landonr/homeThing/docs/groupTDisplay.gif

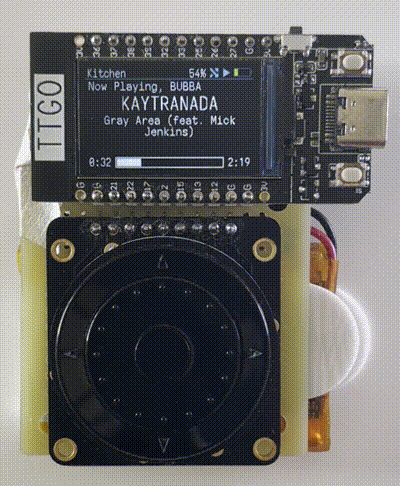
docs/groupTDisplay.gif
