landonr/homeThing/docs/m5stackFire.jpg

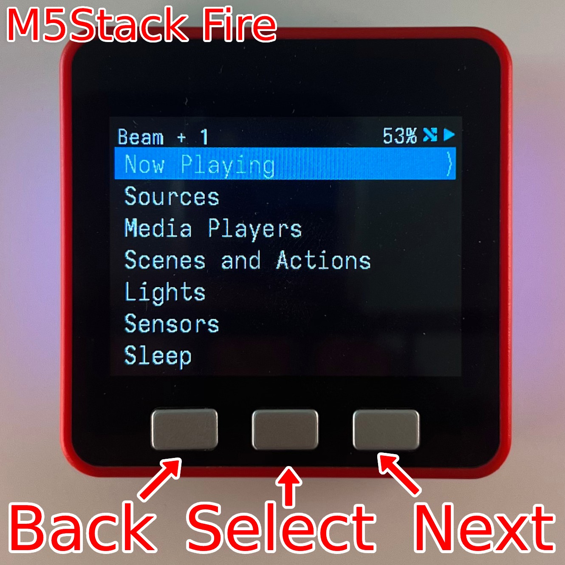
docs/m5stackFire.jpg
