landonr/homeThing/docs/m5StackFireBoot.gif

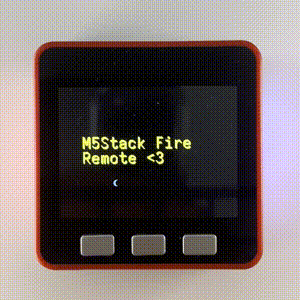
docs/m5StackFireBoot.gif
