landonr/homeThing/docs/nowPlayingOptions.jpg

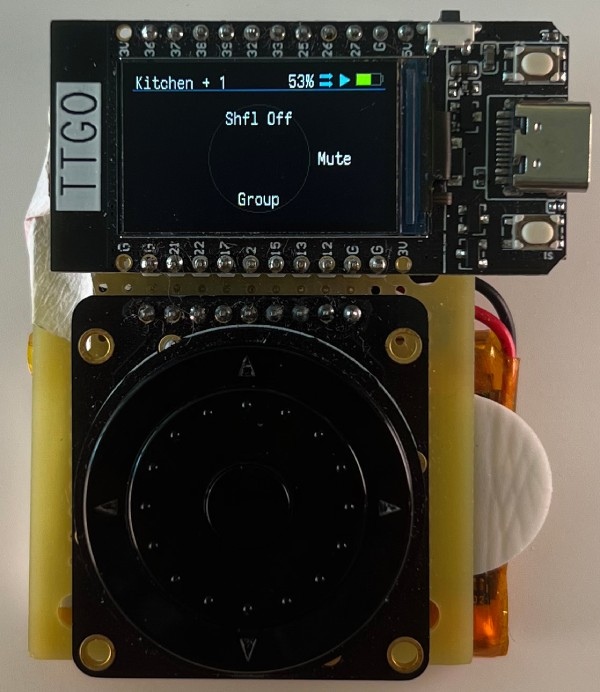
docs/nowPlayingOptions.jpg
