landonr/homeThing/docs/pausePlayFire.gif

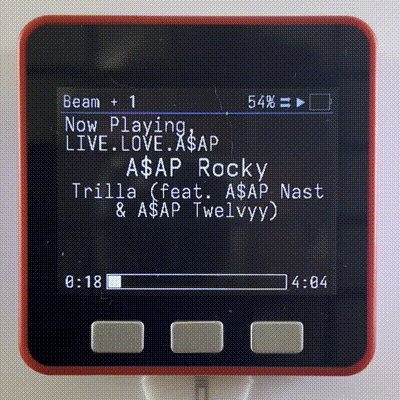
docs/pausePlayFire.gif
