landonr/homeThing/docs/scrollListSelectFire.gif

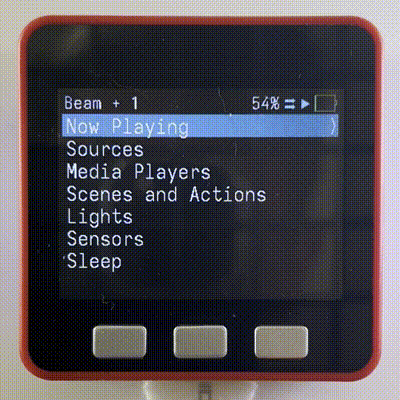
docs/scrollListSelectFire.gif
