landonr/homeThing/docs/sensors.jpg

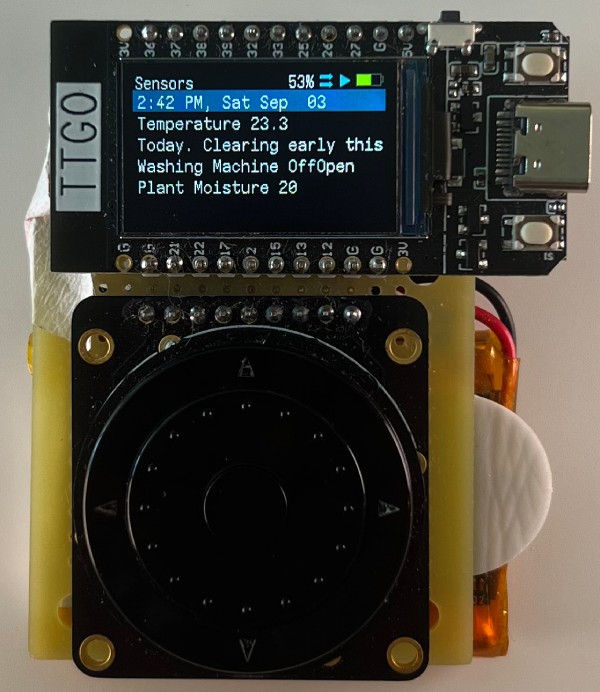
docs/sensors.jpg
