landonr/homeThing/docs/tdisplayOverlay.jpg

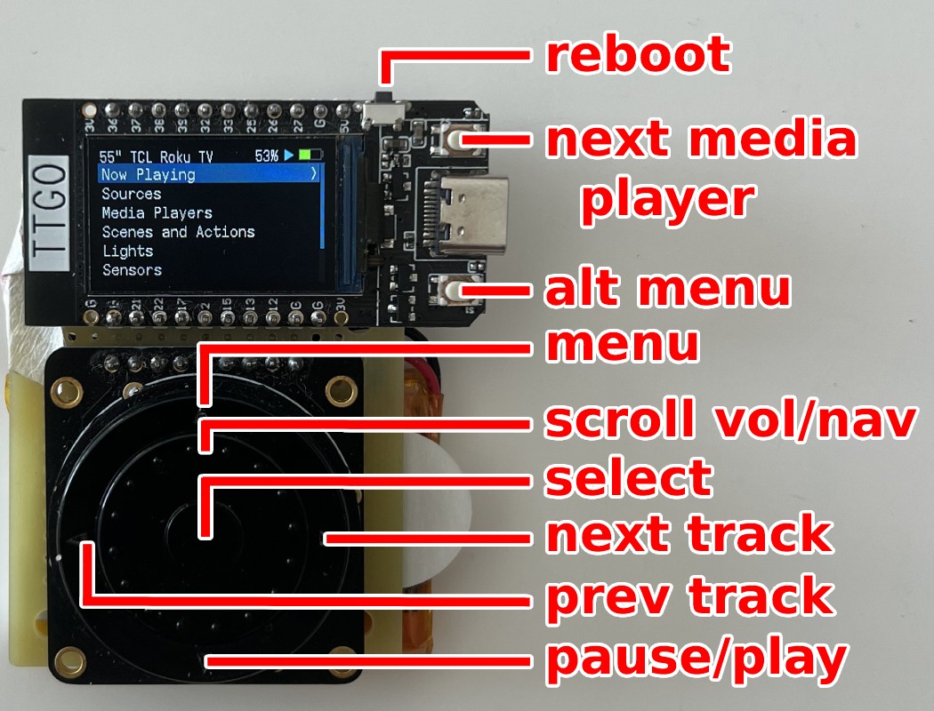
docs/tdisplayOverlay.jpg
