landonr/homeThing/Case Design/tdisplay/Case_v1.1B_--_Button_Set_--_FDM_--_mm.stl

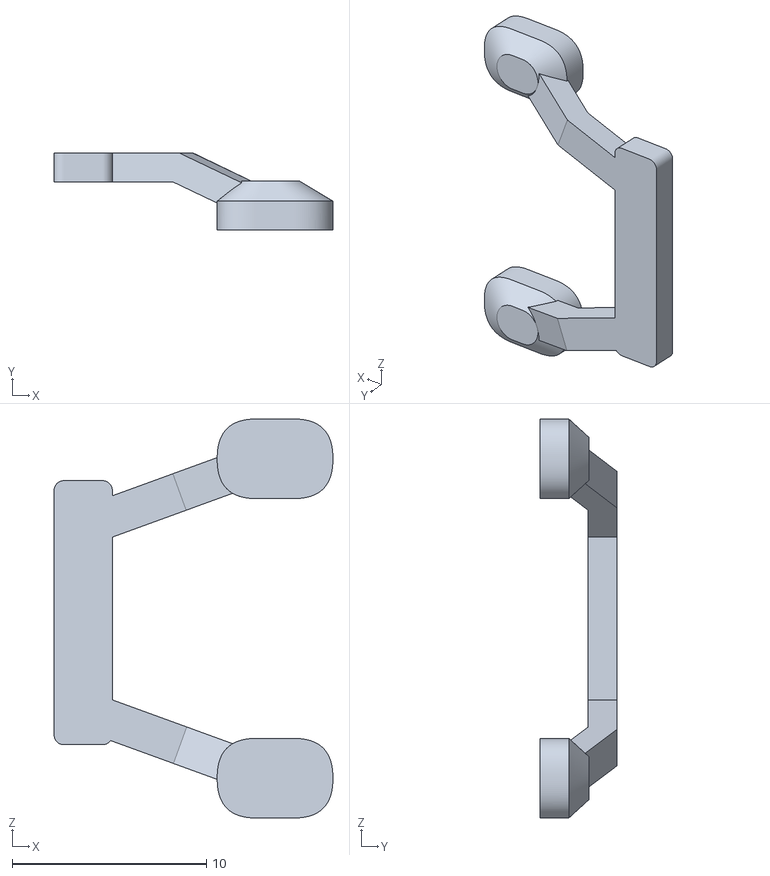
[picture p35: CAD file, 2023-03-23]
Case Design/tdisplay/Case_v1.1B_--_Button_Set_--_FDM_--_mm.stl
14.4 x 3.99 x 20.5
