landonr/homeThing/Case Design/tdisplay/Case_v1.1B_--_Front_Case_--_FDM_--_mm.stl

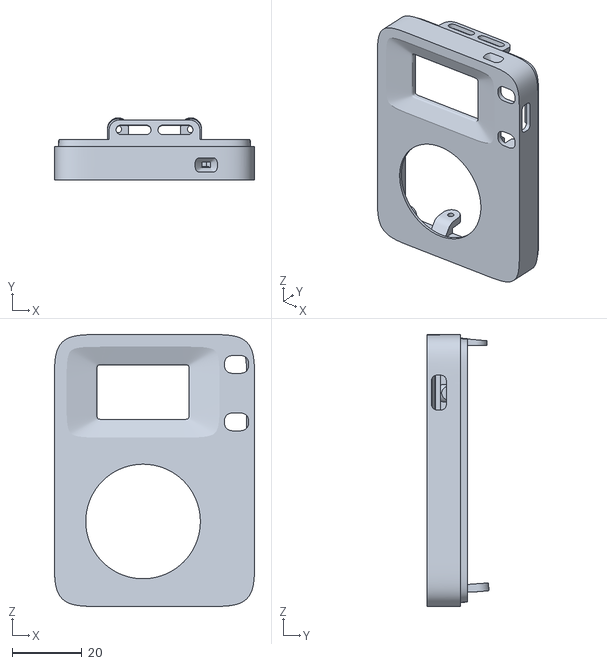
[picture p36: CAD file, 2023-03-23]
Case Design/tdisplay/Case_v1.1B_--_Front_Case_--_FDM_--_mm.stl
57.4 x 17.9 x 77.9
