landonr/homeThing/Case Design/tdisplay/Case_v1.1B_--_Back_Case_--_FDM_--_mm.stl

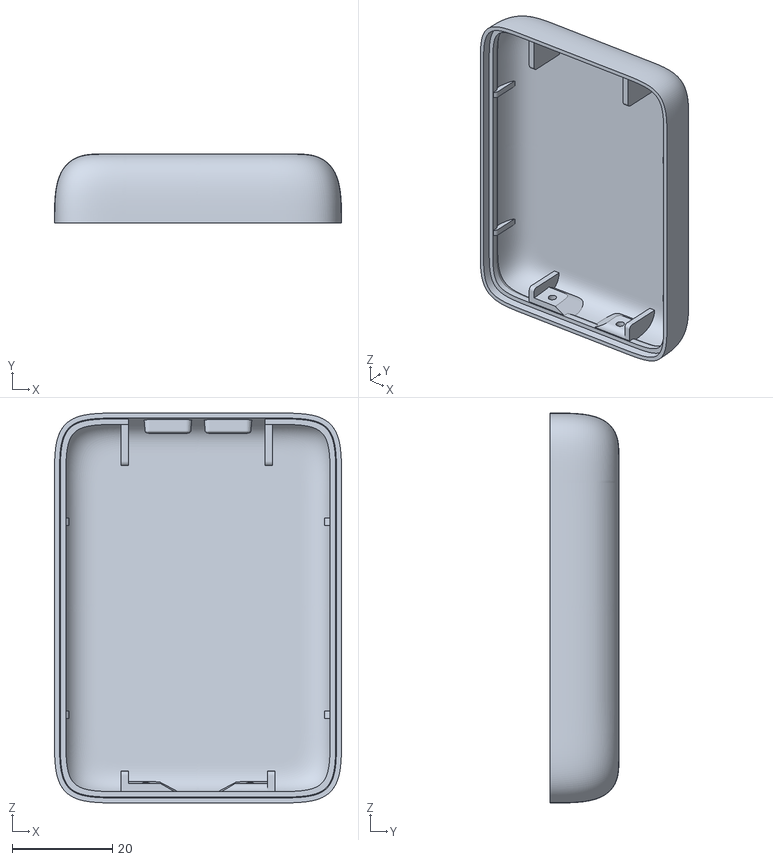
[picture p37: CAD file, 2023-03-23]
Case Design/tdisplay/Case_v1.1B_--_Back_Case_--_FDM_--_mm.stl
57.3 x 13.7 x 77.9
