landonr/homeThing/Case Design/tdisplay/5000mAh battery/bottom view assembled product.jpg

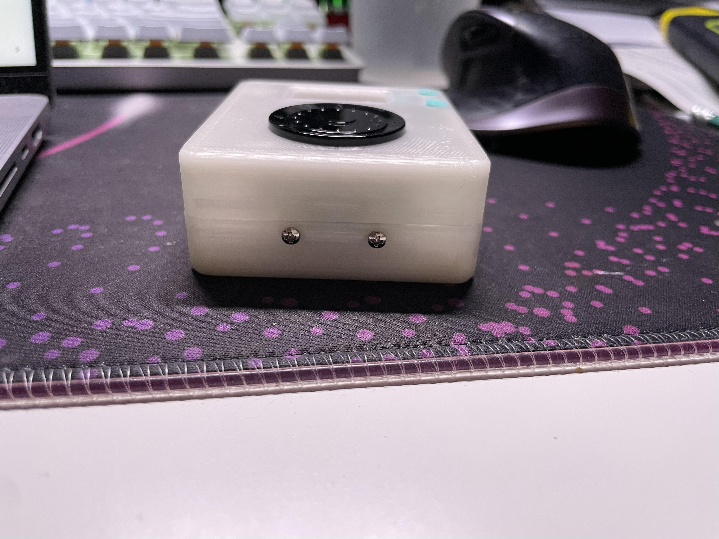
Case Design/tdisplay/5000mAh battery/bottom view assembled product.jpg
