landonr/homeThing/Case Design/tdisplay/5000mAh battery/glow in the dark filament view assembled product.jpg

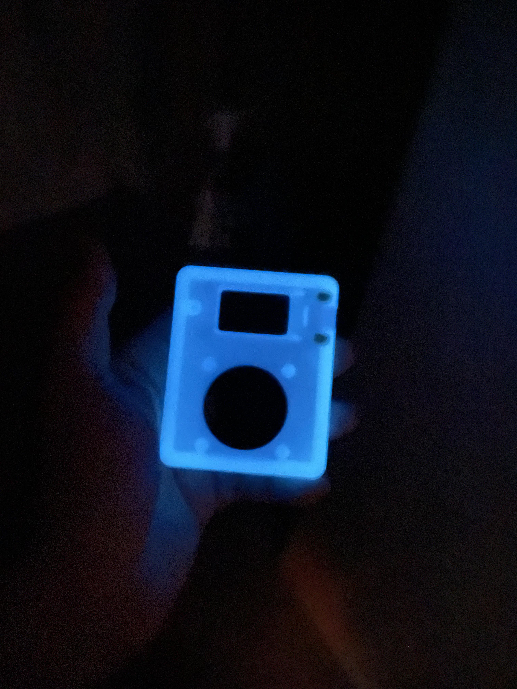
Case Design/tdisplay/5000mAh battery/glow in the dark filament view assembled product.jpg
