landonr/homeThing/Case Design/tdisplay/5000mAh battery/perspective view assembled product.jpg

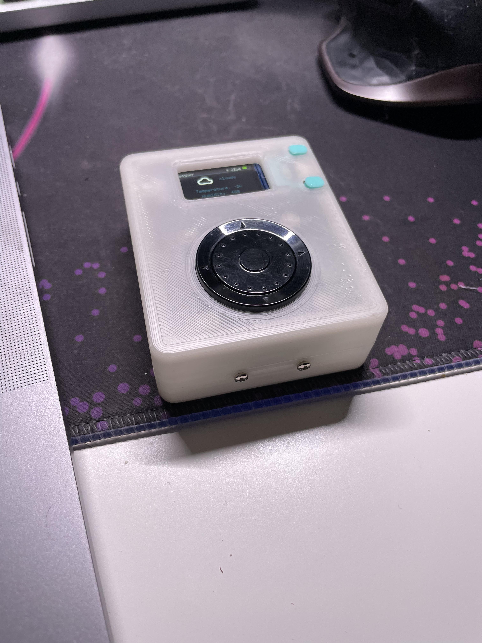
Case Design/tdisplay/5000mAh battery/perspective view assembled product.jpg
