landonr/homeThing/components/homeThing/homeThingMenuHeader.h

#pragma once

#include <string>
#include "esphome/components/homeThing/homeThingMenuScreen.h"
#include "esphome/components/homeThing/homeThingMenuTitle.h"
#include "esphome/components/homeThingDisplayState/homeThingDisplayState.h"

#ifdef USE_MEDIA_PLAYER_GROUP
#include "esphome/components/homeThing/homeThingMenuTitlePlayer.h"
#include "esphome/components/homeThing/homeThingOptionMenu.h"
#include "esphome/components/homeassistant_media_player/HomeAssistantMediaPlayerGroup.h"
#endif

#ifdef USE_BINARY_SENSOR
#include "esphome/components/binary_sensor/binary_sensor.h"
#endif
#include "esphome/components/sensor/sensor.h"
#ifdef USE_TIME
#include "esphome/components/time/real_time_clock.h"
#endif
#include "esphome/core/time.h"

namespace esphome {
namespace homething_menu_base {

class HomeThingMenuHeaderSource {
 public:
  virtual std::string get_header_title() { return "xx"; }
  virtual int draw_header_details(
      int xPos, int yPosOffset, display::Display* display,
      homething_display_state::HomeThingDisplayState* display_state) {
    return 0;
  }
};

class HomeThingMenuHeader {
 public:
  HomeThingMenuHeader(
      display::Display* new_display,
      homething_display_state::HomeThingDisplayState* new_display_state)
      : display_(new_display), display_state_(new_display_state) {}
  void drawHeader(int yPosOffset, const MenuStates activeMenuState);
  void draw_menu_header(HomeThingMenuHeaderSource* header_source);
  void set_battery_percent(sensor::Sensor* battery_percent) {
    battery_percent_ = battery_percent;
  }
#ifdef USE_BINARY_SENSOR
  void set_charging(binary_sensor::BinarySensor* charging) {
    charging_ = charging;
  }
#endif
  void set_active_menu_screen(HomeThingMenuScreen** active_menu_screen) {
    active_menu_screen_ = active_menu_screen;
  }

#ifdef USE_TIME
  void set_time_id(time::RealTimeClock* time_id) { this->esp_time_ = time_id; }
#endif

 private:
  float get_battery_percent() {
    if (battery_percent_ != nullptr && battery_percent_->has_state()) {
      return battery_percent_->state;
    } else {
      return 0;
    }
  }
  bool get_charging() {
#ifdef USE_BINARY_SENSOR
    if (charging_ != nullptr && charging_->has_state()) {
      return charging_->state;
    } else {
      return false;
    }
#else
    return false;
#endif
  }
  void drawHeaderTitleWithString(std::string title, int xPos,
                                 int yPosOffset = 0);
  void drawHeaderTitle(int yPosOffset, const MenuStates activeMenuState);
  int getHeaderTextYPos(int yPosOffset);
  int drawBattery(int oldXPos, int yPosOffset);
  int drawHeaderIcon(std::string title, int xPos, Color iconColor);
#ifdef USE_TIME
  int drawHeaderTime(int oldXPos, int yPosOffset);
#endif

  display::Display* display_{nullptr};
  homething_display_state::HomeThingDisplayState* display_state_{nullptr};
  sensor::Sensor* battery_percent_{nullptr};
#ifdef USE_BINARY_SENSOR
  binary_sensor::BinarySensor* charging_{nullptr};
#endif
#ifdef USE_TIME
  time::RealTimeClock* esp_time_{nullptr};
#endif
  const char* const TAG = "homething.menu.header";
  HomeThingMenuScreen** active_menu_screen_{nullptr};
};

}  // namespace homething_menu_base
}  // namespace esphome
