landonr/homeThing/components/homeThing/version.h

#ifndef COMPONENTS_HOMETHING_VERSION_H_
#define COMPONENTS_HOMETHING_VERSION_H_
#include <string>

namespace esphome {
namespace homething_menu_base {
static const std::string COMPONENTS_HOMETHING_VERSION = "main/2024-05-27";
}
}  // namespace esphome
#endif  // COMPONENTS_HOMETHING_VERSION_H_
