landonr/homeThing/components/homeThing/homeThingMenuBoot.h

#pragma once

#include <algorithm>
#include <memory>
#include <utility>
#include <vector>
#include "esphome/components/display/display.h"
#include "esphome/components/homeThing/homeThingMenuAnimation.h"
#include "esphome/components/homeThing/homeThingMenuHeader.h"
#include "esphome/components/homeThingDisplayState/homeThingDisplayState.h"
#include "esphome/components/homeThingDisplayState/homeThingMenuTextHelpers.h"
#ifdef USE_BINARY_SENSOR
#include "esphome/components/binary_sensor/binary_sensor.h"
#endif

namespace esphome {
namespace homething_menu_base {

enum BootMenuState {
  BOOT_MENU_STATE_START,
  BOOT_MENU_STATE_NETWORK,
  BOOT_MENU_STATE_ACCESS_POINT,
  BOOT_MENU_STATE_API,
  BOOT_MENU_STATE_PLAYERS,
  BOOT_MENU_STATE_COMPLETE
};

enum BootMenuSkipState {
  BOOT_MENU_SKIP_STATE_NONE,
  BOOT_MENU_SKIP_STATE_SLEEP,
  BOOT_MENU_SKIP_STATE_MENU
};

struct HomeThingMenuAnimationConfig {
  int delay_time;
  int animation_length;
};

class HomeThingMenuBootAnimationConfig {
 public:
  HomeThingMenuAnimationConfig logo_config = {2, 6};
  HomeThingMenuAnimationConfig header_config = {8, 20};
  HomeThingMenuAnimationConfig loading_bar_config = {20, 9};

  int total_animation_length() {
    return std::max(
        logo_config.delay_time + logo_config.animation_length,
        std::max(header_config.delay_time + header_config.animation_length,
                 loading_bar_config.delay_time +
                     loading_bar_config.animation_length));
  }
};

class HomeThingMenuBoot {
 public:
  HomeThingMenuBoot(
      display::Display* new_display,
      homething_display_state::HomeThingDisplayState* new_display_state,
      HomeThingMenuHeader* new_header)
      : display_(new_display),
        display_state_(new_display_state),
        header_(new_header) {}
  bool drawBootSequence(const MenuStates activeMenuState);
  BootMenuSkipState bootSequenceCanSkip(const MenuStates activeMenuState);
#ifdef USE_BINARY_SENSOR
  void set_api_connected(binary_sensor::BinarySensor* api_connected) {
    api_connected_ = api_connected;
  }
  void set_media_players_loaded(
      binary_sensor::BinarySensor* media_player_group_sensor);
#endif
  void set_animation(HomeThingMenuAnimation* animation) {
    animation_ = animation;
  }
  bool boot_complete() {
    return get_boot_menu_state() == BOOT_MENU_STATE_COMPLETE;
  }

  template <typename F>
  void add_on_state_callback(F&& callback) {
    this->callback_.add(std::forward<F>(callback));
  }

#ifdef USE_IMAGE
  image::Image* get_launch_image() { return launch_image_; }
  void set_launch_image(image::Image* launch_image) {
    launch_image_ = launch_image;
  }
#endif

 private:
  void drawBootSequenceLoadingBar(int yPosOffset, float progress);
  void drawBootSequenceSkipTitle(int xPos, int imageYPos,
                                 const MenuStates activeMenuState);
  int drawBootSequenceTitleRainbow(int xPos, int yPos,
                                   const MenuStates activeMenuState);
  float bootSequenceLoadingProgress();
  int drawBootSequenceHeader(const MenuStates activeMenuState);
  int drawBootSequenceLoadingBarAnimation();
  int drawBootSequenceLogo(int xPos, int imageYPos);
  int drawBootSequenceTitle(int xPos, int imageYPos,
                            const MenuStates activeMenuState);

  BootMenuState get_boot_menu_state();
  display::Display* display_{nullptr};
  homething_display_state::HomeThingDisplayState* display_state_{nullptr};
  HomeThingMenuAnimation* animation_{nullptr};
  HomeThingMenuHeader* header_{nullptr};
#ifdef USE_BINARY_SENSOR
  binary_sensor::BinarySensor* api_connected_{nullptr};
  binary_sensor::BinarySensor* media_player_group_sensor_{nullptr};
#endif
  const char* const TAG = "homething.boot";
  HomeThingMenuBootAnimationConfig animation_config_ =
      HomeThingMenuBootAnimationConfig();
  CallbackManager<void()> callback_;
  bool boot_animation_complete_ = false;

#ifdef USE_IMAGE
  image::Image* launch_image_{nullptr};
#endif
};

}  // namespace homething_menu_base
}  // namespace esphome
